vincentberthier/meteo_station/hardware/power/meteo_power.kicad_sch

## KiCad design hardware/power/meteo_power.kicad_sch (2026-06-25)

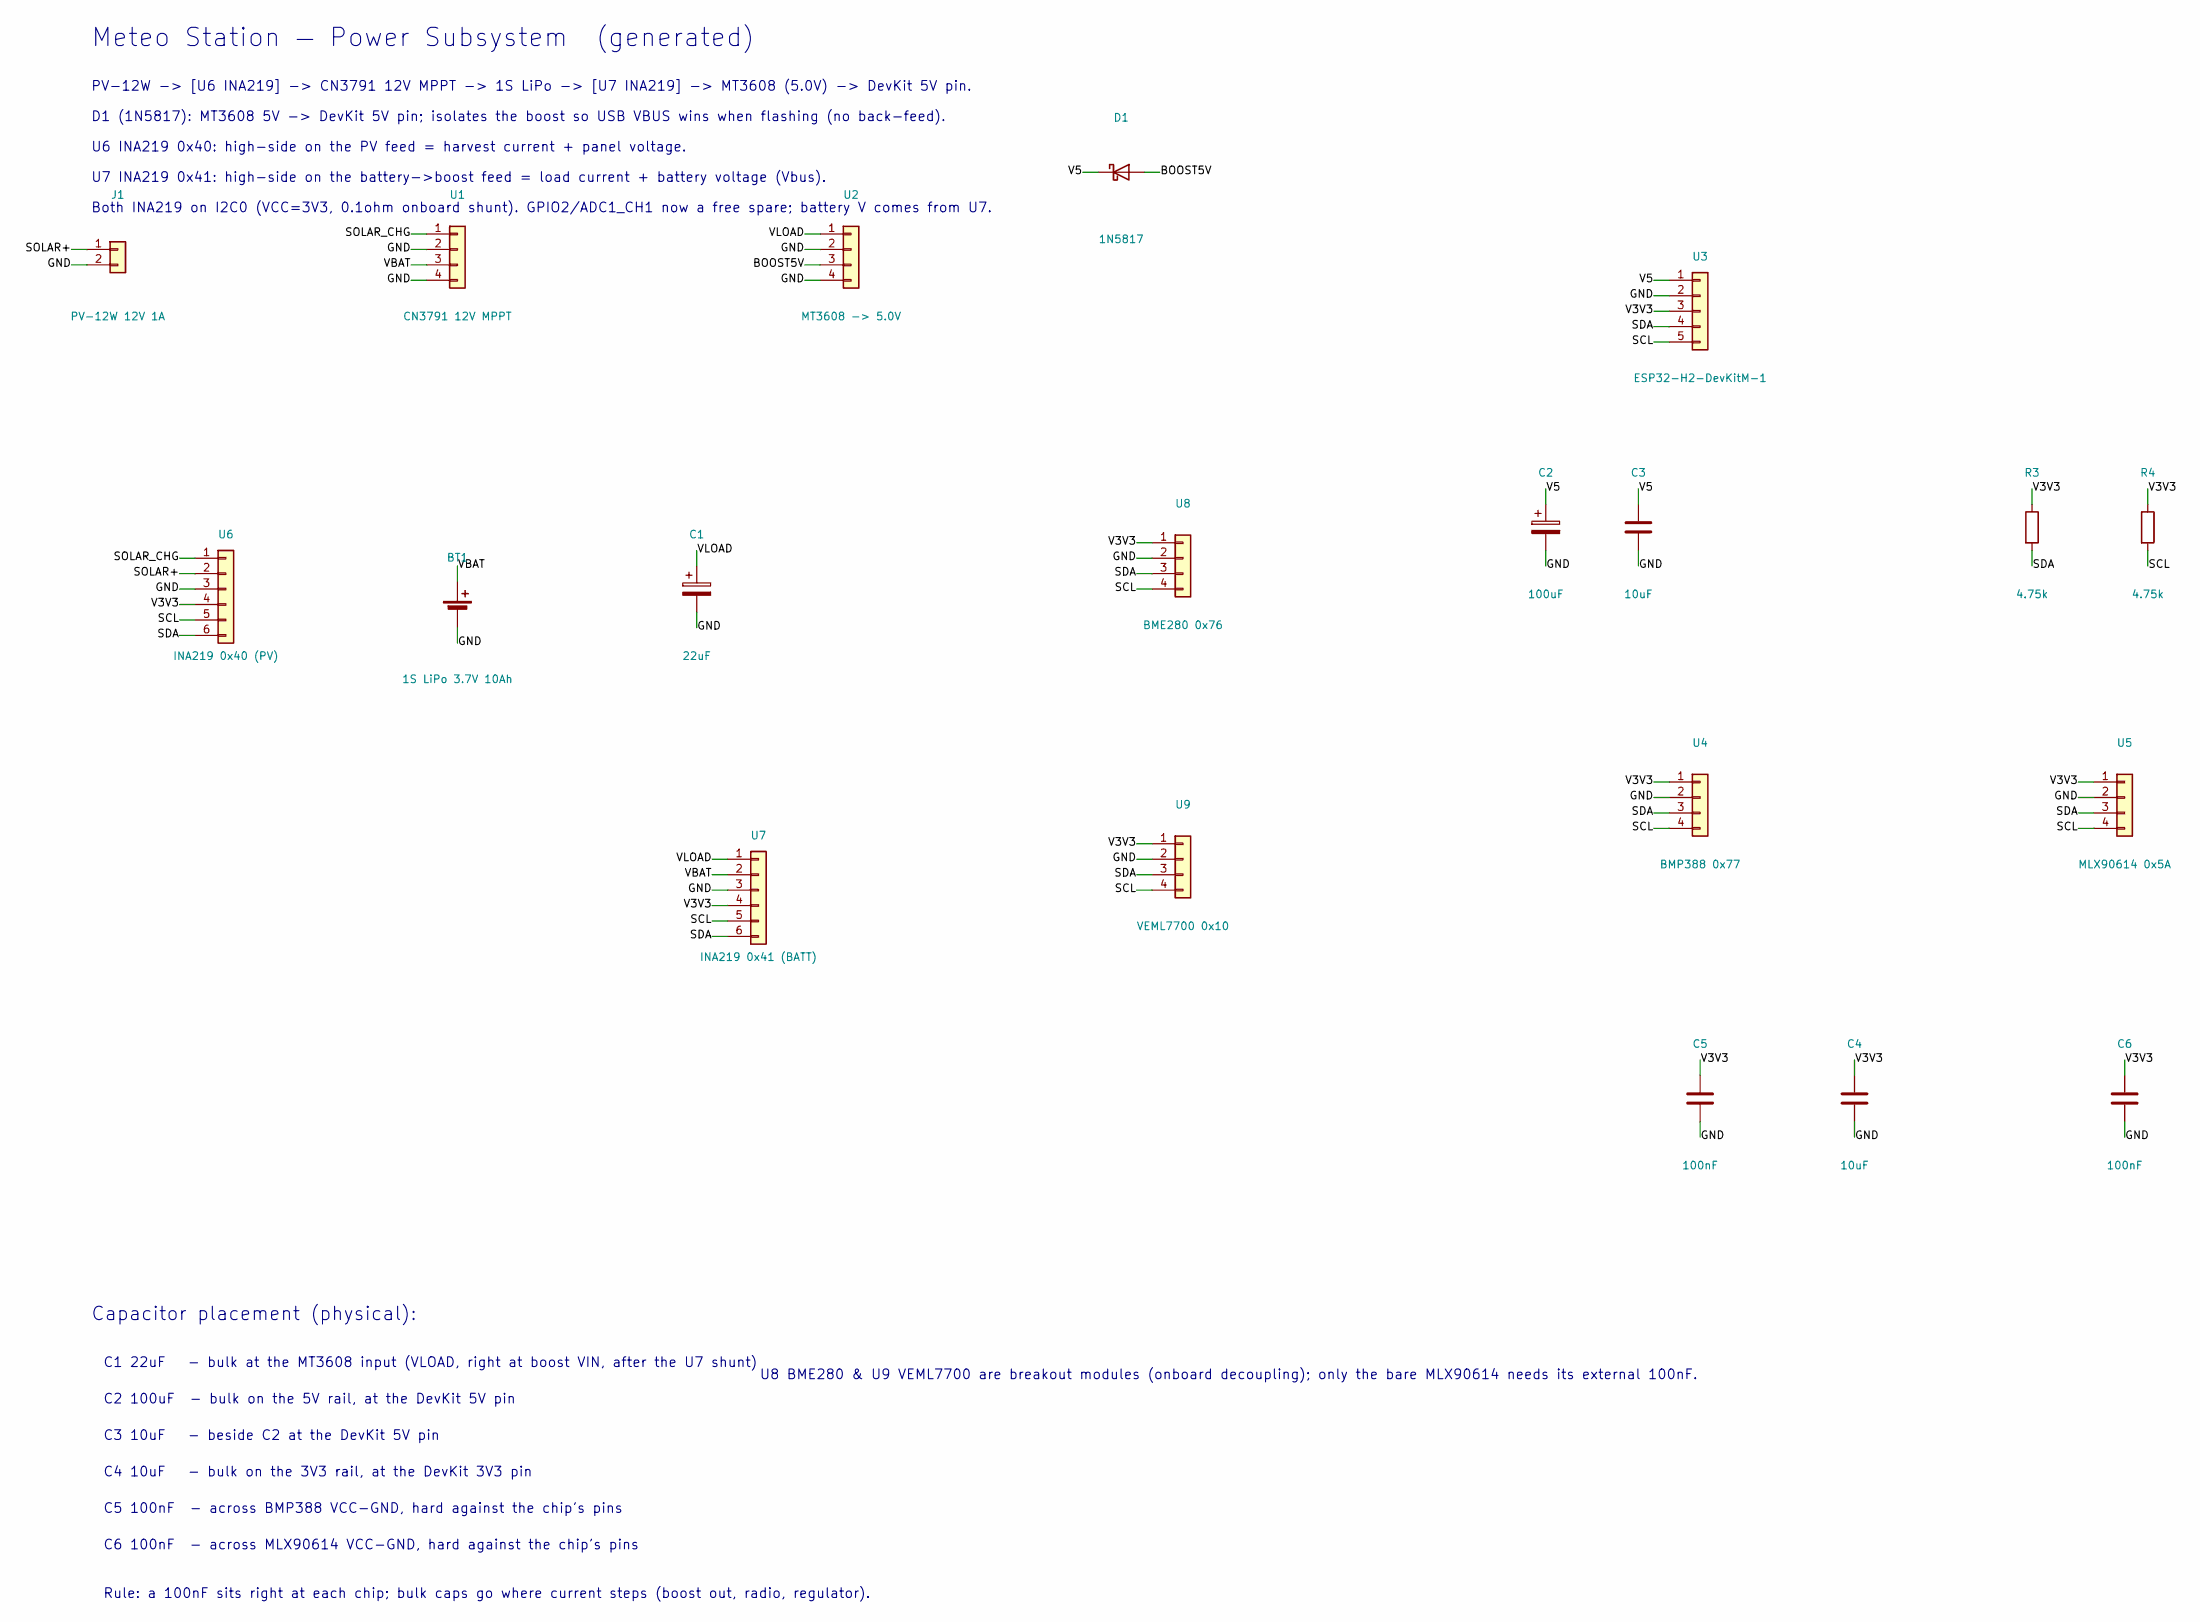
[picture p3: schematic meteo_power.kicad_sch]

Parts:
BT1: 1S LiPo 3.7V 10Ah
C1: 22uF
C2: 100uF
C3, C4: 10uF
C5, C6: 100nF
D1: 1N5817
J1: PV-12W 12V 1A
R3, R4: 4.75k
U1: CN3791 12V MPPT
U2: MT3608 -> 5.0V
U3: ESP32-H2-DevKitM-1
U4: BMP388 0x77
U5: MLX90614 0x5A
U6: INA219 0x40 (PV)
U7: INA219 0x41 (BATT)
U8: BME280 0x76
U9: VEML7700 0x10

Connections:
BOOST5V: D1.2 (A), U2.3
GND: BT1.2 (-), C1.2, C2.2, C3.2, C4.2, C5.2, C6.2, J1.2, U1.2, U1.4, U2.2, U2.4, U3.2, U4.2, U5.2, U6.3, U7.3, U8.2, U9.2
SCL: R4.2, U3.5, U4.4, U5.4, U6.5, U7.5, U8.4, U9.4
SDA: R3.2, U3.4, U4.3, U5.3, U6.6, U7.6, U8.3, U9.3
SOLAR+: J1.1, U6.2
SOLAR_CHG: U1.1, U6.1
V3V3: C4.1, C5.1, C6.1, R3.1, R4.1, U3.3, U4.1, U5.1, U6.4, U7.4, U8.1, U9.1
V5: C2.1, C3.1, D1.1 (K), U3.1
VBAT: BT1.1 (+), U1.3, U7.2
VLOAD: C1.1, U2.1, U7.1

Notes on the sheet:
Meteo Station — Power Subsystem (generated)
PV-12W -> [U6 INA219] -> CN3791 12V MPPT -> 1S LiPo -> [U7 INA219] -> MT3608 (5.0V) -> DevKit 5V pin.
D1 (1N5817): MT3608 5V -> DevKit 5V pin; isolates the boost so USB VBUS wins when flashing (no back-feed).
U6 INA219 0x40: high-side on the PV feed = harvest current + panel voltage.
U7 INA219 0x41: high-side on the battery->boost feed = load current + battery voltage (Vbus).
Both INA219 on I2C0 (VCC=3V3, 0.1ohm onboard shunt). GPIO2/ADC1_CH1 now a free spare; battery V comes from U7.
Capacitor placement (physical):
C1 22uF - bulk at the MT3608 input (VLOAD, right at boost VIN, after the U7 shunt)
C2 100uF - bulk on the 5V rail, at the DevKit 5V pin
C3 10uF - beside C2 at the DevKit 5V pin
C4 10uF - bulk on the 3V3 rail, at the DevKit 3V3 pin
C5 100nF - across BMP388 VCC-GND, hard against the chip's pins
C6 100nF - across MLX90614 VCC-GND, hard against the chip's pins
Rule: a 100nF sits right at each chip; bulk caps go where current steps (boost out, radio, regulator).
U8 BME280 & U9 VEML7700 are breakout modules (onboard decoupling); only the bare MLX90614 needs its external 100nF.
